Shrike-Lab/HomeLab-PDU-V1/ASSEMBLY/CAD/Blanks/10in_Uni-Tray-BLANK.stl.STEP

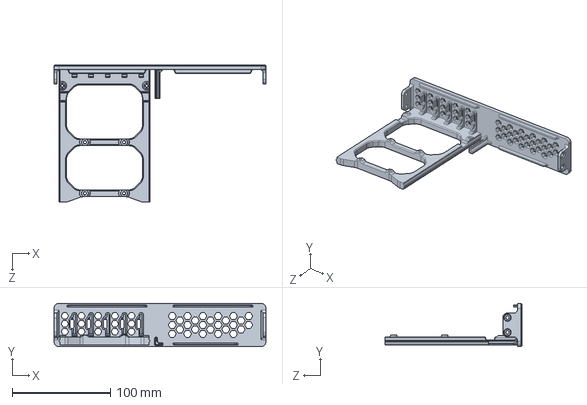
[picture p15: CAD file, 2026-04-01]
ASSEMBLY/CAD/Blanks/10in_Uni-Tray-BLANK.stl.STEP
216.0 x 44.0 x 140.0 mm
