Shrike-Lab/HomeLab-PDU-V1/ASSEMBLY/CAD/Universal/IEC_Bracket.stl

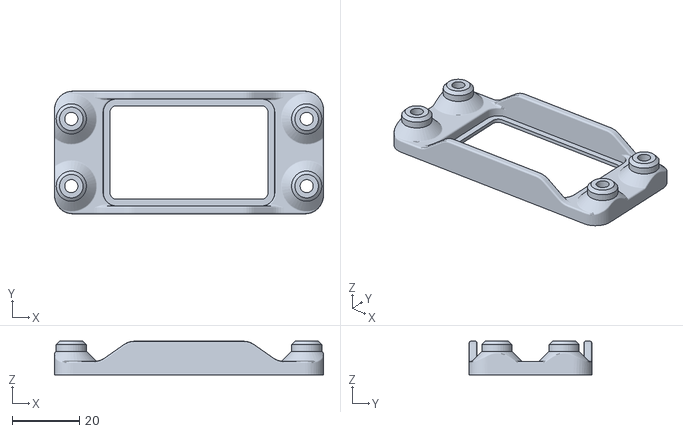
[picture p16: CAD file, 2026-03-31]
ASSEMBLY/CAD/Universal/IEC_Bracket.stl
80.0 x 36.5 x 10.00
