Shrike-Lab/HomeLab-PDU-V1/ASSEMBLY/CAD/19in_Single/19in_Single-Front_2.3mf

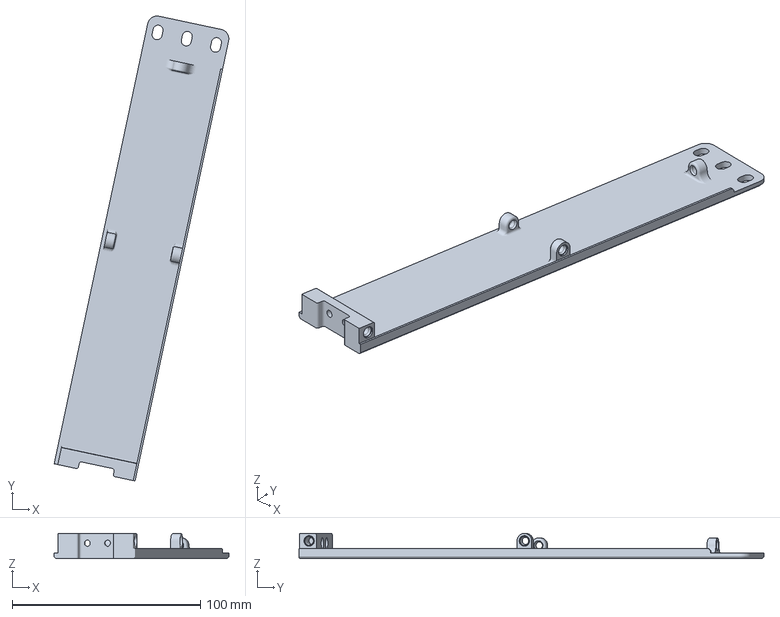
[picture p17: CAD file, 2026-03-31]
ASSEMBLY/CAD/19in_Single/19in_Single-Front_2.3mf
92.9 x 247.3 x 13.4 mm
