Shrike-Lab/HomeLab-PDU-V1/ASSEMBLY/CAD/Universal/PCB_Tray.stl

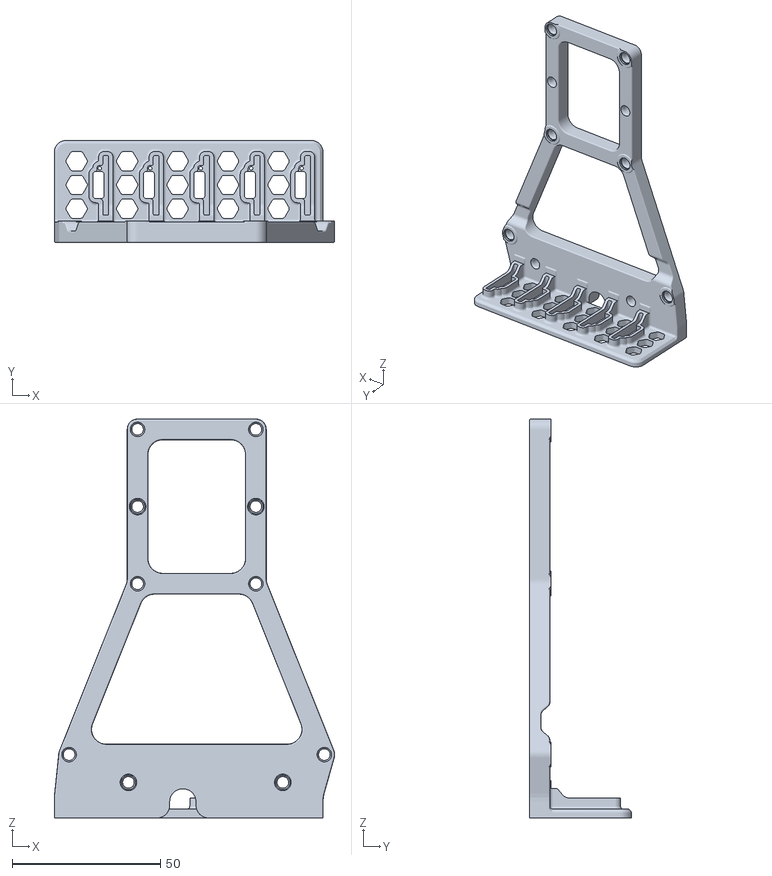
[picture p18: CAD file, 2026-03-31]
ASSEMBLY/CAD/Universal/PCB_Tray.stl
94.5 x 34.4 x 134.4
